coastalwarming/Wireless_mesocosm/Firmware/Mesocosm_firmware_v74/ConfigStore.h

#define CONFIG_FLAG_VALID       0x01
#define CONFIG_FLAG_STATIC_IP   0x02

#define BLYNK_PROV_ERR_NONE     0      // All good
#define BLYNK_PROV_ERR_CONFIG   700    // Invalid config from app (malformed token,etc)
#define BLYNK_PROV_ERR_NETWORK  701    // Could not connect to the router
#define BLYNK_PROV_ERR_CLOUD    702    // Could not connect to the cloud
#define BLYNK_PROV_ERR_TOKEN    703    // Invalid token error (after connection)
#define BLYNK_PROV_ERR_INTERNAL 704    // Other issues (i.e. hardware failure)

struct ConfigStore {
  uint32_t  magic;
  char      version[15];
  uint8_t   flags;

  char      wifiSSID[34];
  char      wifiPass[64];

  char      cloudToken[34];
  char      cloudHost[34];
  uint16_t  cloudPort;

  uint32_t  staticIP;
  uint32_t  staticMask;
  uint32_t  staticGW;
  uint32_t  staticDNS;
  uint32_t  staticDNS2;

  int       last_error;

  void setFlag(uint8_t mask, bool value) {
    if (value) {
      flags |= mask;
    } else {
      flags &= ~mask;
    }
  }

  bool getFlag(uint8_t mask) {
    return (flags & mask) == mask;
  }
} __attribute__((packed));

ConfigStore configStore;

const ConfigStore configDefault = {
  0x626C6E6B,
  BLYNK_FIRMWARE_VERSION,
  0x00,
  
  "",
  "",
  
  "invalid token",
  CONFIG_DEFAULT_SERVER,
  CONFIG_DEFAULT_PORT,
  0,
  BLYNK_PROV_ERR_NONE
};

template<typename T, int size>
void CopyString(const String& s, T(&arr)[size]) {
  s.toCharArray(arr, size);
}

static bool config_load_blnkopt()
{
  static const char blnkopt[] = "blnkopt\0"
    BLYNK_PARAM_KV("ssid" , BLYNK_PARAM_PLACEHOLDER_64
                            BLYNK_PARAM_PLACEHOLDER_64
                            BLYNK_PARAM_PLACEHOLDER_64
                            BLYNK_PARAM_PLACEHOLDER_64)
    BLYNK_PARAM_KV("host" , CONFIG_DEFAULT_SERVER)
    BLYNK_PARAM_KV("port" , BLYNK_TOSTRING(CONFIG_DEFAULT_PORT))
    "\0";

  BlynkParam prov(blnkopt+8, sizeof(blnkopt)-8-2);
  BlynkParam::iterator ssid = prov["ssid"];
  BlynkParam::iterator pass = prov["pass"];
  BlynkParam::iterator auth = prov["auth"];//Troquei o auth por auth_ .
  BlynkParam::iterator host = prov["host"];
  BlynkParam::iterator port = prov["port"];

  if (!(ssid.isValid() && auth.isValid())) {//Troquei o auth por auth_ .
    return false;
  }

  // reset to defaut before loading values from blnkopt
  configStore = configDefault;

  if (ssid.isValid()) { CopyString(ssid.asStr(), configStore.wifiSSID); }
  if (pass.isValid()) { CopyString(pass.asStr(), configStore.wifiPass); }
  if (auth.isValid()) { CopyString(auth.asStr(), configStore.cloudToken); }//Troquei o auth por auth_ .
  if (host.isValid()) { CopyString(host.asStr(), configStore.cloudHost); }
  if (port.isValid()) { configStore.cloudPort = port.asInt(); }

  return true;
}

//#include <Preferences.h>
//Preferences preferences;

void config_load()
{
  memset(&configStore, 0, sizeof(configStore));
  preferences.getBytes("config", &configStore, sizeof(configStore));
  if (configStore.magic != configDefault.magic) {
    DEBUG_PRINT("Using default config.");
    configStore = configDefault;
    return;
  }
}

bool config_save()
{
  preferences.putBytes("config", &configStore, sizeof(configStore));
  DEBUG_PRINT("Configuration stored to flash");
  return true;
}

bool config_init()
{
  preferences.begin("blynk", false);
  config_load();
  return true;
}

void enterResetConfig()
{
  DEBUG_PRINT("Resetting configuration!");
  configStore = configDefault;
  config_save();
  eraseMcuConfig();
  BlynkState::set(MODE_WAIT_CONFIG);
}

void config_set_last_error(int error) {
  // Only set error if not provisioned
  if (!configStore.getFlag(CONFIG_FLAG_VALID)) {
    configStore = configDefault;
    configStore.last_error = error;
    BLYNK_LOG2("Last error code: ", error);
    config_save();
  }
}
