coastalwarming/Wireless_mesocosm/Firmware/Mesocosm_firmware_v74/Console.h

#include <Blynk/BlynkConsole.h>

BlynkConsole    edgentConsole;

void console_init()
{
  edgentConsole.init(BLYNK_PRINT);

  edgentConsole.print("\n>");

  edgentConsole.addCommand("reboot", []() {
    edgentConsole.print(R"json({"status":"OK","msg":"resetting device"})json" "\n");
    delay(100);
    restartMCU();
  });

  edgentConsole.addCommand("config", []() {
    edgentConsole.print(R"json({"status":"OK","msg":"entering configuration mode"})json" "\n");
    BlynkState::set(MODE_WAIT_CONFIG);
  });
//Troquei BLYNK_TEMPLATE_ID por BLYNK_TEMPLATE_ID_
  edgentConsole.addCommand("devinfo", []() {
    edgentConsole.printf(
        R"json({"board":"%s","tmpl_id":"%s","fw_type":"%s","fw_ver":"%s"})json" "\n",
        BLYNK_DEVICE_NAME_,//Troquei BLYNK_DEVICE_NAME por BLYNK_DEVICE_NAME_ .
        BLYNK_TEMPLATE_ID_,
        BLYNK_FIRMWARE_TYPE,
        BLYNK_FIRMWARE_VERSION
    );
  });

  edgentConsole.addCommand("netinfo", []() {
    char ssidBuff[64];
    getWiFiName(ssidBuff, sizeof(ssidBuff));

    byte mac[6] = { 0, };
    WiFi.macAddress(mac);

    edgentConsole.printf(
        R"json({"ssid":"%s","bssid":"%02x:%02x:%02x:%02x:%02x:%02x","rssi":%d})json" "\n",
        ssidBuff,
        mac[5], mac[4], mac[3], mac[2], mac[1], mac[0],
        WiFi.RSSI()
    );
  });

}

BLYNK_WRITE(InternalPinDBG) {
  String cmd = String(param.asStr()) + "\n";
  edgentConsole.runCommand((char*)cmd.c_str());
}
