coastalwarming/Wireless_mesocosm/Firmware/Mesocosm_firmware_v74/SD_Update.ino

// check given FS for valid update.bin and perform update if available
void updateFromFS(fs::FS &fs) {
  File updateBin = fs.open("/update.bin");
  if (updateBin) {
    if (updateBin.isDirectory()) {
      Serial.println("Error, update.bin is not a file");
      updateBin.close();
      return;
    }

    size_t updateSize = updateBin.size();

    if (updateSize > 0) {
      Serial.println("Try to start update");



      performUpdate(updateBin, updateSize);
    }
    else {
      Serial.println("Error, file is empty");
    }

    updateBin.close();

    // whe finished remove the binary from sd card to indicate end of the process
    fs.remove("/update.bin");
    ESP.restart();
  }
  else {
    Serial.println("Could not load update.bin from sd root");
  }
}

void performUpdate(Stream &updateSource, size_t updateSize) {
  if (Update.begin(updateSize)) {
    size_t written = Update.writeStream(updateSource);
    if (written == updateSize) {
      Serial.println("Written : " + String(written) + " successfully");
    }
    else {
      Serial.println("Written only : " + String(written) + "/" + String(updateSize) + ". Retry?");
    }
    if (Update.end()) {
      Serial.println("OTA done!");
      if (Update.isFinished()) {
        Serial.println("Update successfully completed. Rebooting.");

   
      }
      else {
        Serial.println("Update not finished? Something went wrong!");
      }
    }
    else {
      Serial.println("Error Occurred. Error #: " + String(Update.getError()));
    }

  }
  else
  {
    Serial.println("Not enough space to begin OTA");
  }
}
